Wulkop/SliderVolumeMixer/Platine/Fader/Fader.kicad_sch

## KiCad design Platine/Fader/Fader.kicad_sch (2022-12-21)

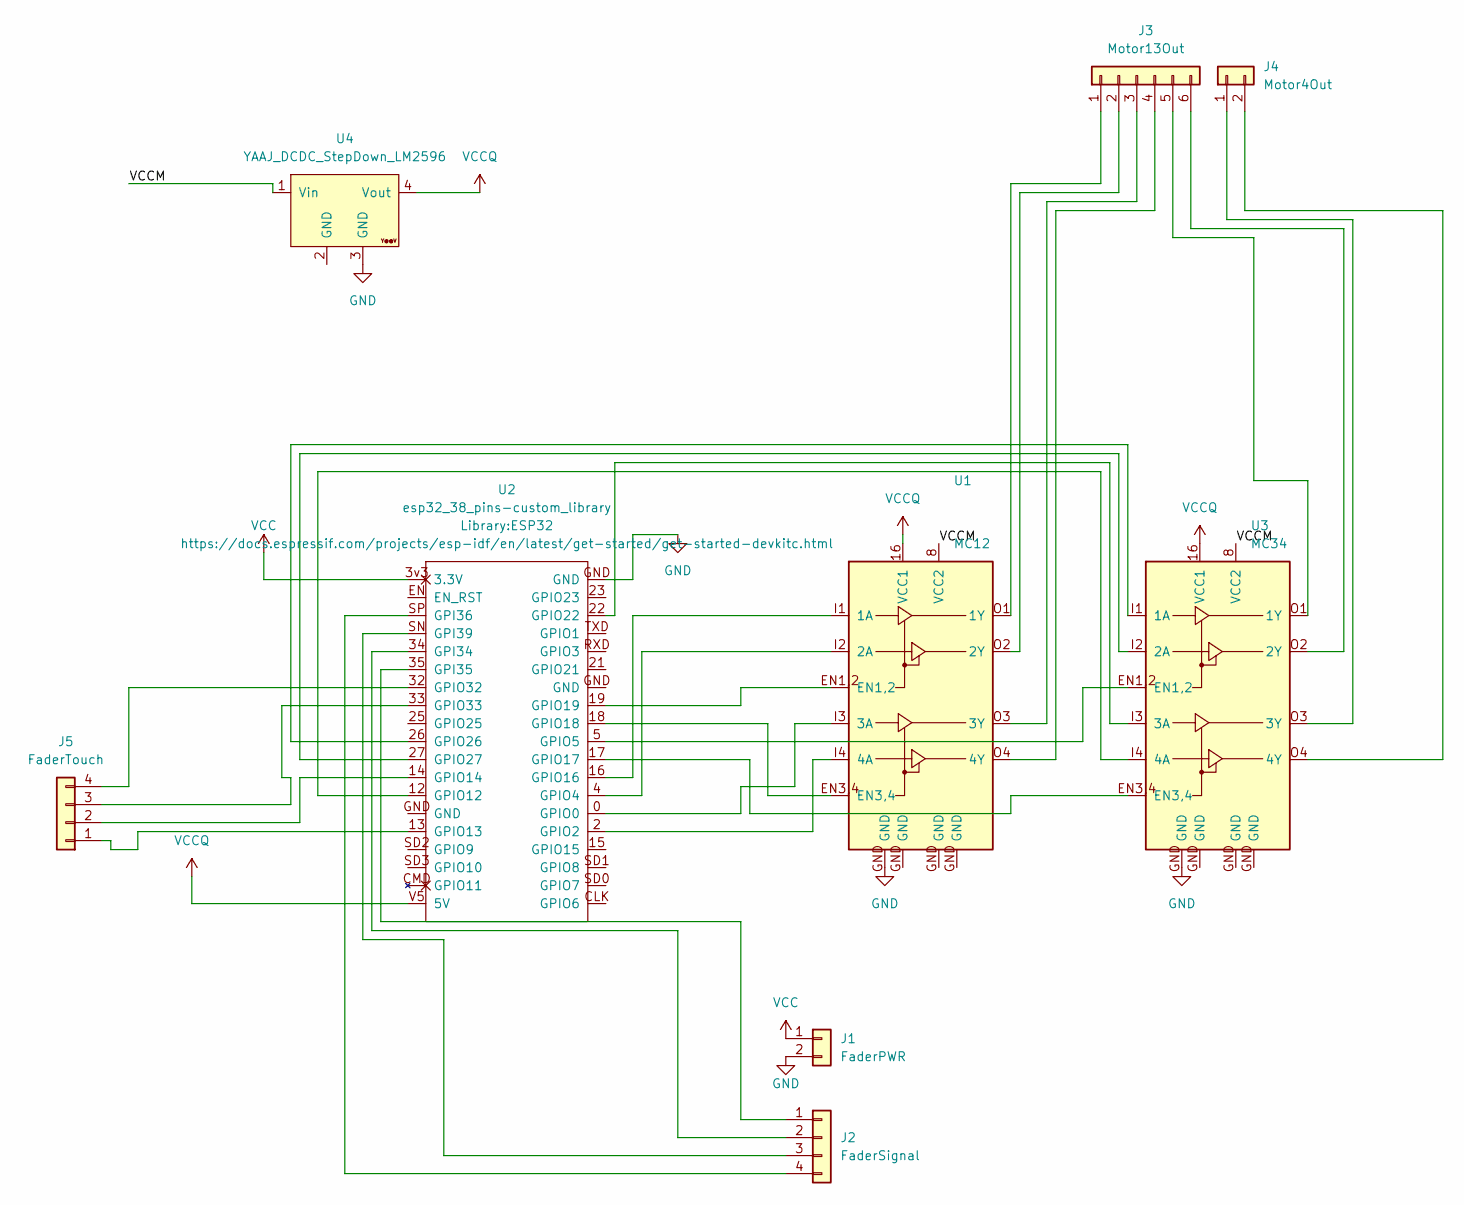
[picture p5: schematic Fader.kicad_sch]

Parts:
J1: FaderPWR; PinHeader_1x02_P2.54mm_Vertical
J2: FaderSignal; PinHeader_1x04_P2.54mm_Vertical
J3: Motor13Out; PinHeader_1x06_P2.54mm_Vertical
J4: Motor4Out; PinHeader_1x02_P2.54mm_Vertical
J5: FaderTouch; PinHeader_1x04_P2.54mm_Vertical
U1: MC12; DIP-16_W7.62mm
U2: esp32_38_pins-custom_library; ESP32
U3: MC34; DIP-16_W7.62mm
U4: YAAJ_DCDC_StepDown_LM2596

Connections:
GND: J1.2, U1.GND, U2.GND, U3.GND, U4.3 (GND)
unnamed: J2.1, U2.35 (GPI35)
unnamed: J2.2, U2.34 (GPI34)
unnamed: J2.3, U2.SN (GPI39)
unnamed: J2.4, U2.SP (GPI36)
unnamed: J3.1, U1.O1 (1Y)
unnamed: J3.2, U1.O2 (2Y)
unnamed: J3.3, U1.O3 (3Y)
unnamed: J3.4, U1.O4 (4Y)
unnamed: J3.5, U3.O1 (1Y)
unnamed: J3.6, U3.O2 (2Y)
unnamed: J4.1, U3.O3 (3Y)
unnamed: J4.2, U3.O4 (4Y)
unnamed: J5.1, U2.13 (GPIO13)
unnamed: J5.2, U2.14 (GPIO14)
unnamed: J5.3, U2.33 (GPIO33)
unnamed: J5.4, U2.32 (GPIO32)
unnamed: U1.EN1,2, U2.19 (GPIO19)
unnamed: U1.EN3,4, U2.18 (GPIO18)
unnamed: U1.I1 (1A), U2.16 (GPIO16)
unnamed: U1.I2 (2A), U2.4 (GPIO4)
unnamed: U1.I3 (3A), U2.0 (GPIO0)
unnamed: U1.I4 (4A), U2.2 (GPIO2)
unnamed: U2.5 (GPIO5), U3.EN1,2
unnamed: U2.12 (GPIO12), U3.I4 (4A)
unnamed: U2.17 (GPIO17), U3.EN3,4
unnamed: U2.22 (GPIO22), U3.I3 (3A)
unnamed: U2.26 (GPIO26), U3.I1 (1A)
unnamed: U2.27 (GPIO27), U3.I2 (2A)
VCC: J1.1, U2.3v3 (3.3V)
VCCM: U1.8 (VCC2), U3.8 (VCC2), U4.1 (Vin)
VCCQ: U1.16 (VCC1), U2.V5 (5V), U3.16 (VCC1), U4.4 (Vout)
